Videocraft10/PetPad/Promo Files/Exports/GitHub QR.png

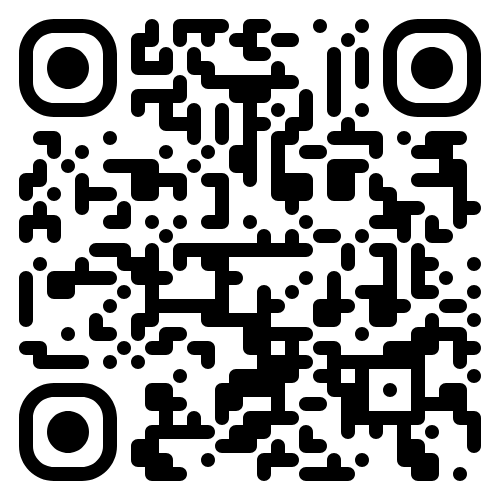
Promo Files/Exports/GitHub QR.png
