Videocraft10/PetPad/Promo Files/Exports/PetPad Main.png

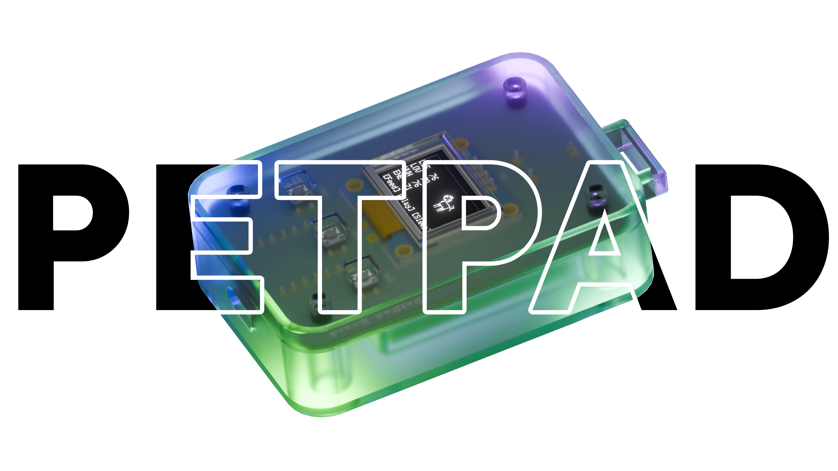
Promo Files/Exports/PetPad Main.png
