Videocraft10/PetPad/Promo Files/Exports/Zine/Videocraft PetPad Zine Background.png

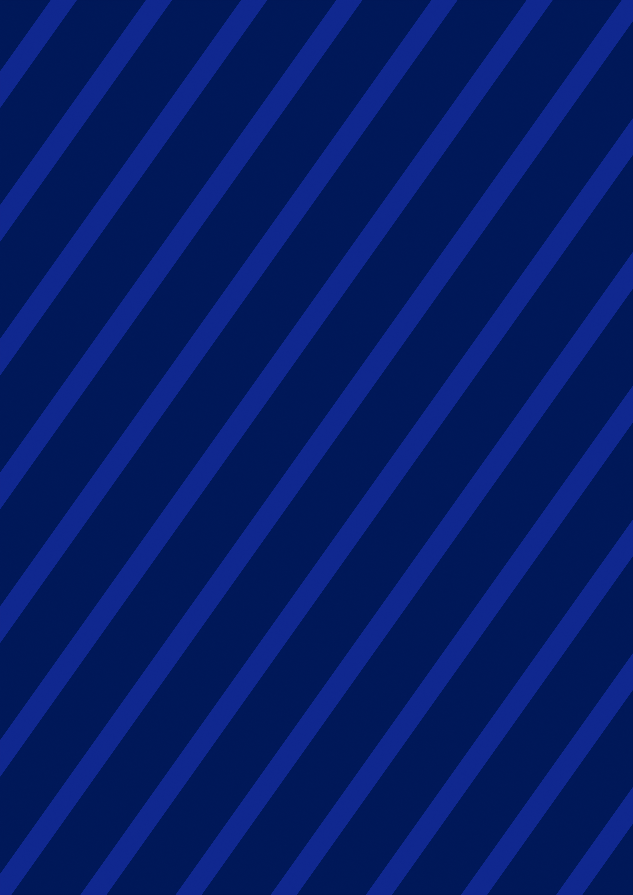
Promo Files/Exports/Zine/Videocraft PetPad Zine Background.png
