Videocraft10/PetPad/Promo Files/Exports/Zine/Videocraft PetPad Zine Cutout.png

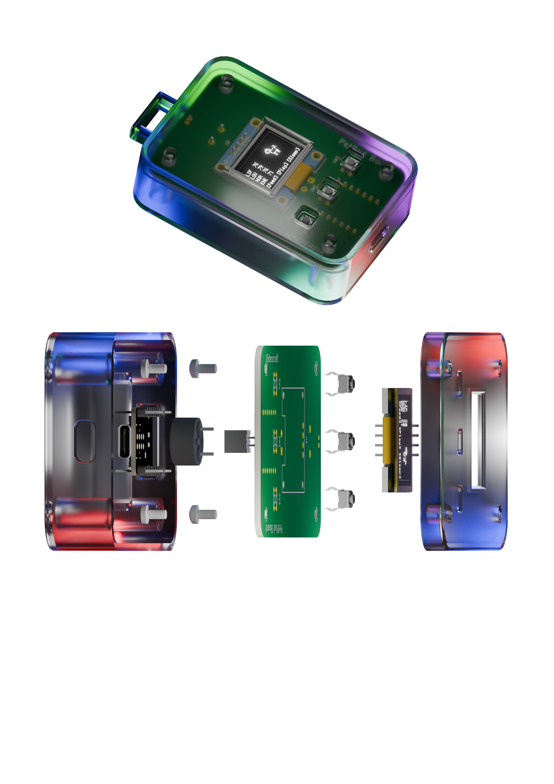
Promo Files/Exports/Zine/Videocraft PetPad Zine Cutout.png
